milan-simanek/3-bldc/sw/comf-cfg.h

#define ComSendChar	UsartSendChar
#define HAVE_COMFCHAR
#define HAVE_COMFHEX1
#define HAVE_COMFHEX2
#define HAVE_COMFHEX4
//#define HAVE_COMFHEX6
//#define HAVE_COMFHEX8

//#define HAVE_COMFIHEX1
//#define HAVE_COMFIHEX2
#define HAVE_COMFIHEX4

//#define HAVE_COMFDEC1B
//#define HAVE_COMFDEC2B
//#define HAVE_COMFDEC02

#define COM_CONVERSIONCHAR	'%'
